ddrown/stm32-input-capture-f031/clients/i2c_registers.h

#ifndef I2C_REGISTERS_H
#define I2C_REGISTERS_H

#define I2C_ADDR 0x4
#define EXPECTED_FREQ 48000000
#define INPUT_CHANNELS 4

// i2c interface
#define I2C_REGISTER_OFFSET_PAGE 31
#define I2C_REGISTER_PAGE1 0
#define I2C_REGISTER_PAGE2 1
#define I2C_REGISTER_PAGE3 2
#define I2C_REGISTER_PAGE4 3
#define I2C_REGISTER_PAGE5 4
#define I2C_REGISTER_VERSION 3

#define SAVE_STATUS_NONE 0
#define SAVE_STATUS_OK 1
#define SAVE_STATUS_ERASE_FAIL 2
#define SAVE_STATUS_WRITE_FAIL 3

#define I2C_REGISTER_PRIMARY_CHANNEL 28
#define I2C_REGISTER_PRIMARY_CHANNEL_HZ 29

struct i2c_registers_type {
  // start 0 len 4
  uint32_t milliseconds_now;
  // start 4 len 4
  uint32_t milliseconds_irq_primary;
  // start 8 len 16
  uint32_t tim2_at_cap[4];
  // start 24 len 4
  uint8_t ch_count[4];
  // start 28 len 1
  uint8_t primary_channel;
  // start 29 len 1
  uint8_t primary_channel_HZ;
  // start 30 len 1
  uint8_t version;
  // start 31 len 1
  uint8_t page_offset;
};

struct i2c_registers_type_page2 {
  uint32_t last_adc_ms;
  uint16_t internal_temp;
  uint16_t internal_vref;
  uint16_t internal_vbat;
  uint16_t ts_cal1;     // internal_temp value at 30C+/-5C @3.3V+/-10mV
  uint16_t ts_cal2;     // internal_temp value at 110C+/-5C @3.3V+/-10mV
  uint16_t vrefint_cal; // internal_vref value at 30C+/-5C @3.3V+/-10mV
  uint8_t reserved[15];
  uint8_t page_offset;
};

// write from tcxo_a to save
#define I2C_PAGE3_WRITE_LENGTH 20
struct i2c_registers_type_page3 {
  /* tcxo_X variables are floats stored as:
   * byte 1: negative sign (1 bit), exponent bits 7-1
   * byte 2: exponent bit 0, mantissa bits 23-17
   * byte 3: mantissa bits 16-8
   * byte 4: mantissa bits 7-0
   * they describe the expected frequency error in ppm:
   * ppm = tcxo_a + tcxo_b * (F - tcxo_d) + tcxo_c * pow(F - tcxo_d, 2)
   * where F is the temperature from the internal_temp sensor in Fahrenheit
   */
  uint32_t tcxo_a;
  uint32_t tcxo_b;
  uint32_t tcxo_c;
  uint32_t tcxo_d;
  uint8_t max_calibration_temp; // F
  int8_t min_calibration_temp;  // F
  uint8_t rmse_fit;             // ppb
  uint8_t save;                 // 1=save new values to flash
  uint8_t save_status;          // see SAVE_STATUS_X

  uint8_t reserved[10];

  uint8_t page_offset;
};

struct tempcomp_data {
  float tcxo_a;
  float tcxo_b;
  float tcxo_c;
  float tcxo_d;
};

#define SET_RTC_DATETIME 1
#define SET_RTC_CALIBRATION 2
#define SET_RTC_SUBSECOND 3

#define CALIBRATION_ADDCLK      0b1000000000
#define CALIBRATION_SUBCLK_MASK 0b0111111111
#define SUBSECOND_ADD1S       0b1000000000000000
#define SUBSECOND_SUBCLK_MASK 0b0111111111111111

struct i2c_registers_type_page4 {
  uint16_t subsecond_div; // number of counts in 1s
  uint16_t subseconds; // read: subseconds (downcount), write: bit 15: +1s, bit 14..0: -N counts/PREDIV_S

  uint32_t datetime; // bits 0..4: day, 5..8: month, 9..14: second, 15..20: minute, 21..25: hour

  uint16_t lse_calibration; // bits 0..8: -N counts/32s, 9: +1count/2^11 (+488.281ppm)
  uint8_t year; // 0-99
  uint8_t set_rtc; // write values SET_RTC_DATETIME, SET_RTC_CALIBRATION, SET_RTC_SUBSECOND
// ^^^ 12 bytes

  uint32_t tim2_rtc_second;
  uint32_t reserved_0;

  uint32_t LSE_millis_irq; // 1pps LSE signal vs TCXO
  uint32_t LSE_tim2_irq;
  uint16_t LSE_tim14_cap;

  uint8_t reserved;
  uint8_t page_offset;
// ^^^ 12+20=32 bytes
};

struct i2c_registers_type_page5 {
  uint32_t cur_tim2;
  uint32_t cur_millis;
  uint32_t backup_register[5];
  uint16_t reserved_0;
  uint8_t reserved_1;
  uint8_t page_offset;
};

void get_i2c_structs(int fd, struct i2c_registers_type *i2c_registers, struct i2c_registers_type_page2 *i2c_registers_page2);
void get_rtc(int fd, struct timeval *setpage, struct i2c_registers_type_page4 *i2c_registers_page4);
void get_timers(int fd, struct timespec *before_setpage, struct timespec *setpage, struct i2c_registers_type_page5 *i2c_registers_page5);
void get_i2c_page3(int fd, struct i2c_registers_type_page3 *i2c_registers_page3, struct tempcomp_data *data);
float last_i2c_time();

#endif
