ddrown/stm32-input-capture-f031/clients/i2c_registers.c

#include <stdint.h>
#include <unistd.h>
#include <stdio.h>
#include <stdlib.h>
#include <sys/time.h>
#include <time.h>

#include "i2c_registers.h"
#include "i2c.h"
#include "float.h"

static float i2c_time = 0;

float last_i2c_time() {
  return i2c_time;
}

void get_rtc(int fd, struct timeval *setpage, struct i2c_registers_type_page4 *i2c_registers_page4) {
  uint8_t set_page[2];

  set_page[0] = I2C_REGISTER_OFFSET_PAGE;
  set_page[1] = I2C_REGISTER_PAGE4;
  lock_i2c(fd);
  write_i2c(fd, set_page, sizeof(set_page));
  gettimeofday(setpage, NULL);
  read_i2c(fd, i2c_registers_page4, sizeof(struct i2c_registers_type_page4));
  unlock_i2c(fd);

  if(i2c_registers_page4->page_offset != I2C_REGISTER_PAGE4) {
    printf("got wrong page offset: %u != %u\n", i2c_registers_page4->page_offset, I2C_REGISTER_PAGE4);
    exit(1);
  }
}

void get_timers(int fd, struct timespec *before_setpage, struct timespec *setpage, struct i2c_registers_type_page5 *i2c_registers_page5) {
  uint8_t set_page[2];

  set_page[0] = I2C_REGISTER_OFFSET_PAGE;
  set_page[1] = I2C_REGISTER_PAGE5;
  lock_i2c(fd);
  clock_gettime(CLOCK_REALTIME, before_setpage);
  write_i2c(fd, set_page, sizeof(set_page));
  clock_gettime(CLOCK_REALTIME, setpage);
  read_i2c(fd, i2c_registers_page5, sizeof(struct i2c_registers_type_page5));
  unlock_i2c(fd);

  if(i2c_registers_page5->page_offset != I2C_REGISTER_PAGE5) {
    printf("got wrong page offset: %u != %u\n", i2c_registers_page5->page_offset, I2C_REGISTER_PAGE5);
    exit(1);
  }
}

void get_i2c_structs(int fd, struct i2c_registers_type *i2c_registers, struct i2c_registers_type_page2 *i2c_registers_page2) {
  uint8_t set_page[2];
  struct timeval start,end;

  gettimeofday(&start, NULL);
  set_page[0] = I2C_REGISTER_OFFSET_PAGE;
  set_page[1] = I2C_REGISTER_PAGE1;
  lock_i2c(fd);
  write_i2c(fd, set_page, sizeof(set_page));
  read_i2c(fd, i2c_registers, sizeof(struct i2c_registers_type));

  if(i2c_registers->page_offset != I2C_REGISTER_PAGE1) {
    printf("got wrong page offset: %u != %u\n", i2c_registers->page_offset, I2C_REGISTER_PAGE1);
    exit(1);
  }

  if(i2c_registers->version != I2C_REGISTER_VERSION) { // TODO: handle compatability
    printf("got unexpected version: %u != %u\n", i2c_registers->version, I2C_REGISTER_VERSION);
    exit(1);
  }

  set_page[0] = I2C_REGISTER_OFFSET_PAGE;
  set_page[1] = I2C_REGISTER_PAGE2;
  write_i2c(fd, set_page, sizeof(set_page));
  read_i2c(fd, i2c_registers_page2, sizeof(struct i2c_registers_type_page2));
  unlock_i2c(fd);

  if(i2c_registers_page2->page_offset != I2C_REGISTER_PAGE2) {
    printf("got wrong page offset: %u != %u\n", i2c_registers_page2->page_offset, I2C_REGISTER_PAGE2);
    exit(1);
  }
  gettimeofday(&end, NULL);

  end.tv_sec -= start.tv_sec;
  if(end.tv_usec < start.tv_usec) {
    end.tv_sec--;
    end.tv_usec = end.tv_usec - start.tv_usec + 1000000;
  } else {
    end.tv_usec = end.tv_usec - start.tv_usec;
  }
  i2c_time = end.tv_sec + end.tv_usec / 1000000.0;
}

void get_i2c_page3(int fd, struct i2c_registers_type_page3 *i2c_registers_page3, struct tempcomp_data *data) {
  uint8_t set_page[2];

  set_page[0] = I2C_REGISTER_OFFSET_PAGE;
  set_page[1] = I2C_REGISTER_PAGE3;
  lock_i2c(fd);
  write_i2c(fd, set_page, sizeof(set_page));
  read_i2c(fd, i2c_registers_page3, sizeof(struct i2c_registers_type_page3));
  unlock_i2c(fd);

  if(i2c_registers_page3->page_offset != I2C_REGISTER_PAGE3) {
    printf("got wrong page offset: %u != %u\n", i2c_registers_page3->page_offset, I2C_REGISTER_PAGE3);
    exit(1);
  }

  data->tcxo_a = ntohf(i2c_registers_page3->tcxo_a);
  data->tcxo_b = ntohf(i2c_registers_page3->tcxo_b);
  data->tcxo_c = ntohf(i2c_registers_page3->tcxo_c);
  data->tcxo_d = ntohf(i2c_registers_page3->tcxo_d);
}
