ddrown/stm32-input-capture-f031/clients/i2c.c

#include <stdio.h>
#include <unistd.h>
#include <errno.h>
#include <stdlib.h>
#include <stdint.h>
#include <sys/types.h>
#include <sys/stat.h>
#include <sys/file.h>
#include <fcntl.h>
#include <sys/ioctl.h>
#include <linux/i2c-dev.h>

#include "i2c.h"

int lock_i2c(int fd) {
  if(flock(fd, LOCK_EX) < 0) {
    perror("flock failed");
    exit(1);
  }

  return fd;
}

int unlock_i2c(int fd) {
  if(flock(fd, LOCK_UN) < 0) {
    perror("flock failed");
    exit(1);
  }

  return fd;
}

uint8_t read_i2c_register(int fd, uint8_t reg) {
  write_i2c(fd, &reg, 1);

  read_i2c(fd, &reg, 1);
  return reg;
}

void write_i2c_register(int fd, uint8_t reg, uint8_t val) {
  uint8_t data[2];

  data[0] = reg;
  data[1] = val;

  write_i2c(fd, &data, 2);
}

void write_i2c(int fd, void *buffer, ssize_t len) {
  ssize_t status;

  status = write(fd, buffer, len);
  if(status < 0) {
    perror("write to i2c failed");

    // is this from an interrupt on the stm32 side and the pi not supporting clock stretching?
    // happens on roughly 1/200000 requests
    if(errno == EIO) {
      usleep(100);
      status = write(fd, buffer, len);
      if(status < 0) {
        perror("write to i2c failed again");
        exit(1);
      }
    } else {
      exit(1);
    }
  }
  if(status != len) {
    fprintf(stderr,"write not %zu bytes: %zu\n", len, status);
    exit(1);
  }
}

void read_i2c(int fd, void *buffer, ssize_t len) {
  ssize_t status;

  status = read(fd, buffer, len);
  if(status < 0) {
    perror("read to i2c failed");
    exit(1);
  }
  if(status != len) {
    fprintf(stderr,"read not %zu bytes: %zu\n", len, status);
    exit(1);
  }
}

int open_i2c(uint16_t i2c_addr) {
  int fd;

  fd = open(I2C_BUS_DEV, O_RDWR);
  if (fd < 0) {
    perror("open " I2C_BUS_DEV " failed");
    exit(1);
  }

  if (ioctl(fd, I2C_SLAVE, i2c_addr) < 0) {
    perror("ioctl i2c slave addr failed");
    exit(1);
  }

  return fd;
}
