ddrown/stm32-input-capture-f031/Inc/timer.h

#ifndef TIMER_H
#define TIMER_H

extern RTC_HandleTypeDef hrtc;
extern TIM_HandleTypeDef htim2;
extern TIM_HandleTypeDef htim14;

#define DEFAULT_SOURCE_HZ 50

void print_timer_status();
void timer_start();
void set_rtc_registers();
void set_rtc(uint8_t data);

void set_page5_registers();
void rtc_start();

#endif
