ddrown/stm32-input-capture-f031/clients/adc_calc.c

#include <stdint.h>
#include <stdio.h>
#include <sys/time.h>

#include "i2c_registers.h"
#include "adc_calc.h"
#include "vref_calc.h"
#include "avg.h"

#define AVERAGE_SAMPLES 60

static float temps[AVERAGE_SAMPLES];
static int8_t adc_index = -1;

static uint32_t last_adc = 0;

float last_temp() {
  return avg_f(temps, adc_index+1);
}

void adc_header() {
  printf("int-temp vref vbat");
}

void adc_print() {
  printf("%.4f ", last_temp()*9/5.0+32.0);
  printf("%.5f ", last_vref());
  printf("%.5f ", last_vbat());
}

void add_adc_data(const struct i2c_registers_type *i2c_registers, const struct i2c_registers_type_page2 *i2c_registers_page2) {
  if(i2c_registers_page2->last_adc_ms == last_adc) {
    return;
  }

  if(adc_index < (AVERAGE_SAMPLES-1)) {
    adc_index++;
  } else {
    for(uint8_t i = 0; i < (AVERAGE_SAMPLES-1); i++) {
      temps[i] = temps[i+1];
    }
  }

  last_adc = i2c_registers_page2->last_adc_ms;

  add_power_data(i2c_registers_page2);

  float vref = last_vref();

  float temp_voltage = i2c_registers_page2->internal_temp/4096.0*vref;
  float v_30C = i2c_registers_page2->ts_cal1/4096.0*3.3;
  float v_110C = i2c_registers_page2->ts_cal2/4096.0*3.3;

  temps[adc_index] = (temp_voltage - v_30C) * (110 - 30) / (v_110C-v_30C) + 30.0;
}
